cgallizzi/inkterface/design/feather-board.png

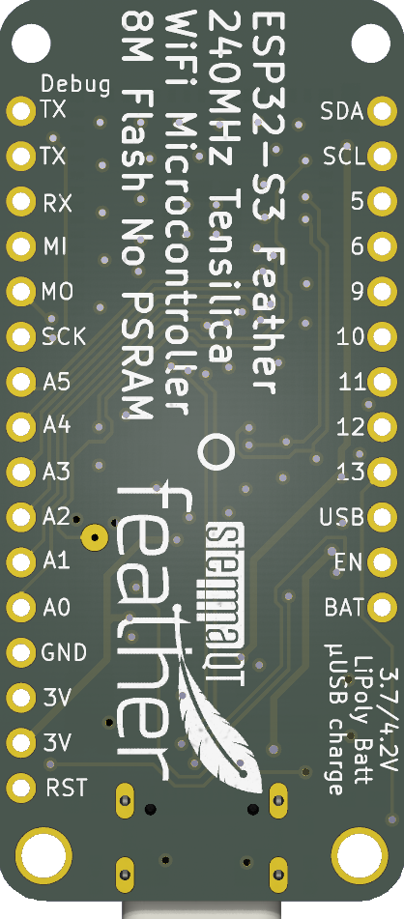
design/feather-board.png
