cgallizzi/inkterface/design/store-assets/Header_Capsule.png

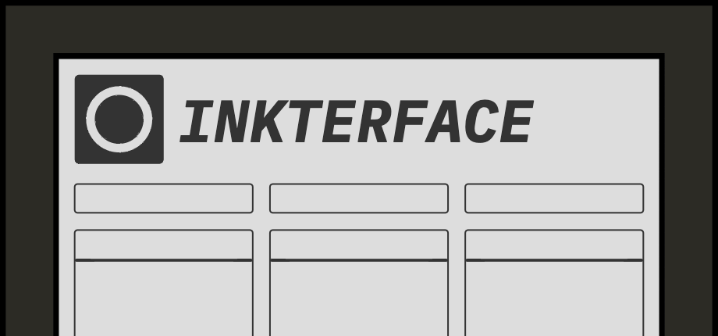
design/store-assets/Header_Capsule.png
