cgallizzi/inkterface/design/store-assets/Library_Capsule.png

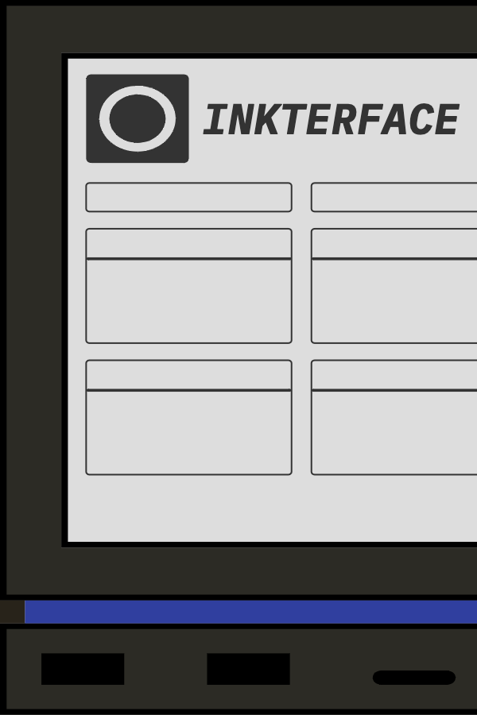
design/store-assets/Library_Capsule.png
