cgallizzi/inkterface/design/store-assets/Machine_Status.png

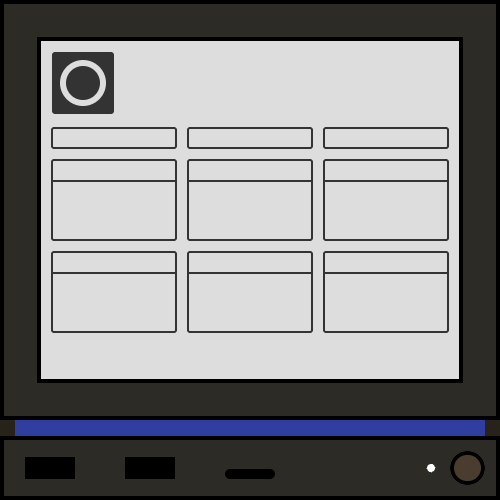
design/store-assets/Machine_Status.png
