cgallizzi/inkterface/design/store-assets/Small_Capsule.png

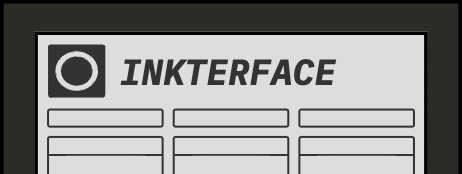
design/store-assets/Small_Capsule.png
