cgallizzi/inkterface/design/store-assets/Vertical_Capsule.png

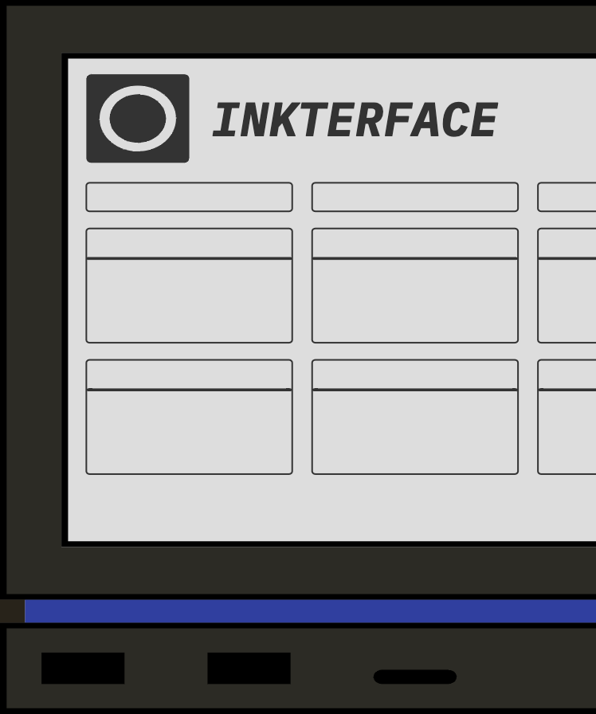
design/store-assets/Vertical_Capsule.png
