cgallizzi/inkterface/resources/gaben.png

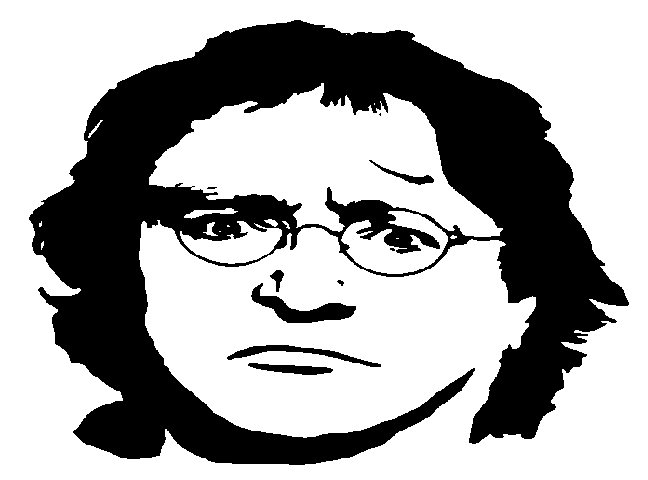
resources/gaben.png
