cgallizzi/inkterface/include/panel-state.hpp

#ifndef PANEL_STATE_HPP
#define PANEL_STATE_HPP

#include <algorithm>
#include <chrono>
#include <functional>
#include <limits>

#include <QObject>
#include <QPointF>
#include <QPointer>
#include <QSettings>
#include <QTimer>

#include "artwork.hpp"
#include "steam.hpp"
#include "sysstats.hpp"

#define PANEL_UPDATE_INTERVAL 2000
#define PANEL_POINT_DEPTH 20
#define PANEL_READOUT_COUNT 3
#define PANEL_SPARK_COUNT 6
#define PANEL_FIELD_COUNT (PANEL_READOUT_COUNT + PANEL_SPARK_COUNT)

using namespace Qt::Literals::StringLiterals;
using DblGetter = std::function<double()>;
using StrGetter = std::function<QString()>;
using Formatter = std::function<QString(double)>;

inline int64_t NOW_MS()
{
    return std::chrono::duration_cast<std::chrono::milliseconds>(
               std::chrono::system_clock::now().time_since_epoch())
        .count();
}

class PanelCollector : public QObject
{
    Q_OBJECT

    Q_PROPERTY(QString displayName READ displayName CONSTANT)
    Q_PROPERTY(QString panelName READ panelName CONSTANT)
    Q_PROPERTY(QString description READ description CONSTANT)
    Q_PROPERTY(bool hasDbl READ hasDbl CONSTANT)
    Q_PROPERTY(bool hasStr READ hasStr CONSTANT)

  public:
    explicit PanelCollector(const QString &disp, const QString &panel, const QString &desc,
                            DblGetter dg = nullptr, StrGetter sg = nullptr, Formatter fmt = nullptr,
                            QObject *parent = nullptr)
        : QObject(parent)
        , m_displayName(disp)
        , m_panelName(panel)
        , m_description(desc)
        , m_dblGetter(dg)
        , m_strGetter(sg)
        , m_formatter(fmt)
    {
        if (hasDbl() && m_formatter == nullptr) {
            m_formatter = [](double value) -> QString { return QString::number(value, 'f', 0); };
        }
    }

    const QString &displayName() const { return m_displayName; }
    const QString &panelName() const { return m_panelName; }
    const QString &description() const { return m_description; }
    bool hasDbl() const { return m_dblGetter != nullptr; }
    Q_INVOKABLE double getDbl(bool *ok = nullptr)
    {
        bool status = false;
        double result = 0;
        if (m_dblGetter) {
            status = true;
            result = m_dblGetter();
        }
        if (ok != nullptr) {
            *ok = status;
        }
        return result;
    }
    bool hasStr() const { return m_strGetter != nullptr || m_formatter != nullptr; }
    Q_INVOKABLE QString getStr(bool *ok = nullptr)
    {
        bool status = false;
        QString result;
        if (m_strGetter) {
            status = true;
            result = m_strGetter();
        } else if (m_dblGetter && m_formatter) {
            status = true;
            result = m_formatter(m_dblGetter());
        }
        if (ok != nullptr) {
            *ok = status;
        }
        return result;
    }

  private:
    QString m_displayName;
    QString m_panelName;
    QString m_description;
    DblGetter m_dblGetter;
    StrGetter m_strGetter;
    Formatter m_formatter;
};

class PanelField : public QObject
{
    Q_OBJECT

    Q_PROPERTY(QString key READ key NOTIFY readoutChanged)
    Q_PROPERTY(QString val READ val NOTIFY readoutChanged)

    Q_PROPERTY(int depth READ depth NOTIFY pointsChanged)
    Q_PROPERTY(QList<QPointF> points READ points NOTIFY pointsChanged)
    Q_PROPERTY(double xMax READ xMax NOTIFY pointsChanged)
    Q_PROPERTY(double xMin READ xMin NOTIFY pointsChanged)
    Q_PROPERTY(double yMax READ yMax NOTIFY pointsChanged)
    Q_PROPERTY(double yMin READ yMin NOTIFY pointsChanged)

    Q_PROPERTY(PanelCollector *collector READ collector WRITE setCollector NOTIFY collectorChanged)

  public:
    explicit PanelField(const int &index, const double &depth = 0, QObject *parent = nullptr)
        : QObject(parent)
        , m_index(index)
        , m_depth(depth)
    {
    }

    const QString &key() const { return m_key; }
    const QString &val() const { return m_val; }
    const int &depth() const { return m_depth; }
    const QList<QPointF> &points() const { return m_points; }
    const double &xMax() const { return m_xMax; }
    const double &xMin() const { return m_xMin; }
    const double &yMax() const { return m_yMax; }
    const double &yMin() const { return m_yMin; }
    QPointer<PanelCollector> collector() const { return m_collector; }

    void setCollector(QPointer<PanelCollector> collector)
    {
        if (m_collector != collector) {
            m_collector = collector;
            QSettings settings;
            settings.setValue(u"field%1Collector"_s.arg(QString::number(m_index)),
                              m_collector ? m_collector->displayName() : u""_s);
            emit collectorChanged();
            clear();
            if (m_collector) {
                m_key = m_collector->panelName();
                m_val = m_collector->getStr();
            }
            emit readoutChanged();
            emit pointsChanged();
        }
    }

    bool collect(const double &x = 0)
    {
        if (!m_collector)
            return false;
        QString k = m_collector->panelName();
        QString v = m_collector->getStr();
        bool changed = k != m_key || v != m_val;
        m_key = k;
        m_val = v;
        if (changed) {
            emit readoutChanged();
        }
        if (m_depth && m_collector->hasDbl()) {
            changed = true; // when we collect a new point it's always a change
            append(x, m_collector->getDbl());
            emit pointsChanged();
        }
        return changed;
    }

  signals:
    void readoutChanged();
    void pointsChanged();
    void collectorChanged();

  private:
    int m_index = 0;
    QString m_key;
    QString m_val;
    int m_depth = 20;
    QList<QPointF> m_points;
    double m_xMax = 0;
    double m_xMin = 0;
    double m_yMax = 0;
    double m_yMin = 0;
    QPointer<PanelCollector> m_collector;

    void append(const double &x, const double &y)
    {
        m_points.emplace_back(x, y);
        while (m_points.size() > m_depth) {
            m_points.pop_front();
        }
        // slow, recalc max/min, but we keep so few points it's not critical
        m_xMax = std::numeric_limits<double>::lowest();
        m_xMin = std::numeric_limits<double>::max();
        m_yMax = std::numeric_limits<double>::lowest();
        m_yMin = std::numeric_limits<double>::max();
        for (const auto &point : std::as_const(m_points)) {
            m_xMax = std::max(m_xMax, point.x());
            m_xMin = std::min(m_xMin, point.x());
            m_yMax = std::max(m_yMax, point.y());
            m_yMin = std::min(m_yMin, point.y());
        }
    }

    void clear()
    {
        m_key = u""_s;
        m_val = u""_s;
        m_points.clear();
        m_xMax = 0;
        m_xMin = 0;
        m_yMax = 0;
        m_yMin = 0;
    }
};

class PanelState : public QObject
{
    Q_OBJECT

    Q_PROPERTY(bool dirty READ dirty NOTIFY dataChanged)
    Q_PROPERTY(QString topLine READ topLine NOTIFY dataChanged)
    Q_PROPERTY(QString midLine READ midLine NOTIFY dataChanged)
    Q_PROPERTY(QString botLine READ botLine NOTIFY dataChanged)
    Q_PROPERTY(QList<PanelField *> fields READ fields NOTIFY fieldsChanged)
    Q_PROPERTY(QList<PanelCollector *> collectors READ collectors NOTIFY collectorsChanged)
    Q_PROPERTY(bool artworkEnabled READ artworkEnabled WRITE setArtworkEnabled NOTIFY
                   artworkEnabledChanged)

  public:
    explicit PanelState(QObject *parent = nullptr)
        : QObject(parent)
        , m_steam(new steam::Steam(this))
        , m_stats(new SysStats(this))
        , m_artwork(new Artwork(m_steam, this))
        , m_updateTimer(new QTimer(this))
    {
        // str only collectors
        registerCollector(u"OS Version"_s, u"OS"_s, u"Host operating system version."_s,
                          std::bind(&SysStats::getOSVersion, m_stats));
        registerCollector(u"BIOS Version"_s, u"BIOS"_s, u"Host BIOS version."_s,
                          std::bind(&SysStats::getBIOSVersion, m_stats));
        registerCollector(u"Steam Version"_s, u"STEAM"_s, u"Host Steam version."_s,
                          std::bind(&steam::Steam::steamVersion, m_steam));
        // double collectors that can be spark graphed
        registerCollector(u"App Count"_s, u"APPS"_s, u"Number of apps installed on the host."_s,
                          std::bind(&steam::Steam::installedAppCount, m_steam));
        registerCollector(u"Fan RPM"_s, u"FAN"_s, u"Host machine fan RPM."_s,
                          std::bind(&SysStats::getFanRPM, m_stats),
                          [](double v) { return u"%1 RPM"_s.arg(QString::number(v, 'f', 0)); });
        registerCollector(u"GPU Clock"_s, u"GPU SCLK"_s, u"GPU core clock speed in GHz."_s,
                          std::bind(&SysStats::getGPUSCLK, m_stats),
                          [](double v) { return u"%1 GHz"_s.arg(QString::number(v, 'f', 1)); });
        registerCollector(u"GPU Memory Clock"_s, u"GPU MCLK"_s, u"GPU memory clock speed in MHz."_s,
                          std::bind(&SysStats::getGPUSCLK, m_stats),
                          [](double v) { return u"%1 MHz"_s.arg(QString::number(v, 'f', 1)); });
        registerCollector(u"GPU Voltage"_s, u"GPU"_s, u"GPU core rail voltage."_s,
                          std::bind(&SysStats::getGPUV, m_stats),
                          [](double v) { return u"%1 V"_s.arg(QString::number(v, 'f', 3)); });
        registerCollector(u"GPU Power"_s, u"GPU"_s, u"GPU power consumption in Watts."_s,
                          std::bind(&SysStats::getGPUW, m_stats),
                          [](double v) { return u"%1 W"_s.arg(QString::number(v, 'f', 1)); });
        registerCollector(u"GPU Temperature"_s, u"GPU"_s, u"GPU junction temperature in C."_s,
                          std::bind(&SysStats::getGPUTemp, m_stats),
                          [](double v) { return u"%1 C"_s.arg(QString::number(v, 'f', 1)); });
        registerCollector(u"GPU Memory Temperature"_s, u"GPU MEM"_s,
                          u"GPU memory temperature in C."_s,
                          std::bind(&SysStats::getGPUMemTemp, m_stats),
                          [](double v) { return u"%1 C"_s.arg(QString::number(v, 'f', 1)); });
        registerCollector(u"GPU Memory"_s, u"GPU MEM"_s, u"GPU memory usage percent."_s,
                          std::bind(&SysStats::getGPUMemPerc, m_stats),
                          [](double v) { return u"%1%"_s.arg(QString::number(v, 'f', 0)); });
        registerCollector(u"GPU"_s, u"GPU"_s, u"GPU usage percent."_s,
                          std::bind(&SysStats::getGPUPerc, m_stats),
                          [](double v) { return u"%1%"_s.arg(QString::number(v, 'f', 0)); });
        registerCollector(u"SSD Temperature"_s, u"SSD"_s, u"SSD temperature in C."_s,
                          std::bind(&SysStats::getSSDTemp, m_stats),
                          [](double v) { return u"%1 C"_s.arg(QString::number(v, 'f', 1)); });
        registerCollector(u"CPU Temperature"_s, u"CPU"_s, u"CPU temperature in C."_s,
                          std::bind(&SysStats::getCPUTemp, m_stats),
                          [](double v) { return u"%1 C"_s.arg(QString::number(v, 'f', 1)); });
        registerCollector(u"CPU"_s, u"CPU"_s, u"CPU usage percent."_s,
                          std::bind(&SysStats::getCPUPerc, m_stats),
                          [](double v) { return u"%1%"_s.arg(QString::number(v, 'f', 0)); });
        registerCollector(u"CPU Frequency"_s, u"CPU"_s, u"Average CPU core frequency in GHz."_s,
                          std::bind(&SysStats::getCPUCLK, m_stats),
                          [](double v) { return u"%1 GHz"_s.arg(QString::number(v, 'f', 1)); });
        registerCollector(u"Memory"_s, u"MEM"_s, u"System memory usage percent."_s,
                          std::bind(&SysStats::getRAMPerc, m_stats),
                          [](double v) { return u"%1%"_s.arg(QString::number(v, 'f', 0)); });
        registerCollector(u"Uptime"_s, u"UPTIME"_s, u"System uptime in seconds."_s,
                          std::bind(&SysStats::getUptime, m_stats),
                          [](double v) { return u"%1 S"_s.arg(QString::number(v, 'f', 0)); });
        registerCollector(u"Game Time"_s, u"PLAYED"_s,
                          u"Total playtime of the currently running game."_s, [this]() -> QString {
                              const auto &app = m_steam->runningApp();
                              if (app.appid.isEmpty()) {
                                  return u"--"_s;
                              }
                              const double minutes = m_steam->appPlaytimeMinutes(app.appid);
                              if (minutes < 0) {
                                  return u"--"_s;
                              } else if (minutes < 60) {
                                  return u"%1 MIN"_s.arg(QString::number(minutes, 'f', 0));
                              }
                              return u"%1 HRS"_s.arg(QString::number(minutes / 60.0, 'f', 1));
                          });
        registerCollector(u"Achievements"_s, u"ACHIEVE"_s,
                          u"Achievements unlocked in the currently running game."_s,
                          [this]() -> QString {
                              const auto &app = m_steam->runningApp();
                              const auto counts = m_steam->achievements(app.appid);
                              if (app.appid.isEmpty() || counts.second <= 0) {
                                  return u"--"_s;
                              }
                              return u"%1/%2"_s.arg(QString::number(counts.first),
                                                    QString::number(counts.second));
                          });

        /* other ideas for things to track/display:
         *  active download progress as discrete bar
         *  quote of the day
         *  gabe/gnomekyle faces
         *  steampal-chan face
         *  clock (analog and digital, updates every minute)
         *  portal sentry eye
         *  companion cube
         *  literal easter egg
         *  weather display (need to pickup location or allow setting location)
         *  top style readout (likely top n-processes aggregated over like 30+ seconds)
         *  show connected controllers, just steam controller initially, other HID devices
         *      could be identified later or added by community
         */

        connect(m_steam, &steam::Steam::appStarted, this, &PanelState::onAppStarted);
        connect(m_steam, &steam::Steam::appStopped, this, &PanelState::onAppStopped);
        connect(m_steam, &steam::Steam::achievementsUpdated, this,
                &PanelState::onAchievementsUpdated);
        connect(m_artwork, &Artwork::frameReady, this, &PanelState::artworkFrame);
        m_steam->watchConsoleLog(true);

        // TODO: allow configuring different numbers/layouts of fields
        PanelField *field = nullptr;
        for (int i = 0; i < PANEL_FIELD_COUNT; ++i) {
            if (i < PANEL_READOUT_COUNT) {
                field = new PanelField(i, 0, this);
            } else {
                field = new PanelField(i, PANEL_POINT_DEPTH, this);
            }
            m_fields.append(field);
        }
        connect(m_updateTimer, &QTimer::timeout, this, &PanelState::updateState);
        m_updateTimer->setInterval(PANEL_UPDATE_INTERVAL);
        m_updateTimer->setSingleShot(false);
        updateState();
        m_updateTimer->start();
    }

    bool dirty() const { return m_dirty; }
    const QString &topLine() const { return m_topLine; }
    const QString &midLine() const { return m_midLine; }
    const QString &botLine() const { return m_botLine; }
    const QList<PanelField *> fields() const { return m_fields; }
    const QList<PanelCollector *> collectors() const { return m_collectors; }

    void registerCollector(const QString &displayName, const QString &panelName,
                           const QString &description, DblGetter getter, Formatter fmt = nullptr)
    {
        auto collector =
            new PanelCollector(displayName, panelName, description, getter, nullptr, fmt, this);
        m_collectors.append(collector);
        m_collectorMap[displayName] = collector;
        emit collectorsChanged();
    }
    void registerCollector(const QString &displayName, const QString &panelName,
                           const QString &description, StrGetter getter)
    {
        auto collector =
            new PanelCollector(displayName, panelName, description, nullptr, getter, nullptr, this);
        m_collectors.append(collector);
        m_collectorMap[displayName] = collector;
        emit collectorsChanged();
    }

    bool artworkEnabled() const
    {
        QSettings settings;
        return settings.value(u"artworkEnabled"_s, true).toBool();
    }
    void setArtworkEnabled(bool enabled)
    {
        if (enabled == artworkEnabled()) {
            return;
        }
        QSettings settings;
        settings.setValue(u"artworkEnabled"_s, enabled);
        emit artworkEnabledChanged();
        const auto &app = m_steam->runningApp();
        if (!enabled) {
            emit artworkClear();
        } else if (!app.appid.isEmpty()) {
            m_artwork->composeForApp(app, m_steam->appPlaytimeMinutes(app.appid),
                                     m_steam->achievements(app.appid));
        }
    }

  signals:
    void dataChanged();
    void fieldsChanged();
    void collectorsChanged();
    void artworkEnabledChanged();
    // a composed 1bpp frame ready to be pushed to the panel
    void artworkFrame(QByteArray bits, quint16 width, quint16 height);
    // the panel should fall back to the telemetry layout
    void artworkClear();

  public slots:
    void start() { m_updateTimer->start(); }
    void stop() { m_updateTimer->stop(); }
    void updateState()
    {
        bool changed = linkFieldCollectors();

        // top line is hostname from machine
        // TODO: allow configuring this
        changed |= m_topLine != m_stats->getHostName();
        m_topLine = m_stats->getHostName();

        // mid line is the most recent steam user
        // TODO: allow configuring this
        changed |= m_midLine != m_steam->currentUser();
        m_midLine = m_steam->currentUser();

        // bottom line is currently running app info
        // TODO: allow configuring this
        // TODO: add full utf-8 support to the e-ink font
        QString botLine;
        auto app = m_steam->runningApp();
        for (QChar c : std::as_const(app.name)) {
            if (c.unicode() <= 127) {
                botLine.append(c);
            }
        }
        changed |= m_botLine != botLine;
        m_botLine = botLine;

        // collect new data into fields (for all fields that have collectors)
        double x = NOW_MS();
        for (auto field : std::as_const(m_fields)) {
            changed |= field->collect(x);
        }

        if (changed) {
            m_dirty = true;
            emit dataChanged();
        }
    }

  private slots:
    void onAppStarted(steam::App details)
    {
        m_steam->fetchAchievements(details.appid);
        if (artworkEnabled()) {
            m_artwork->composeForApp(details, m_steam->appPlaytimeMinutes(details.appid),
                                     m_steam->achievements(details.appid));
        }
        updateState();
    }
    void onAppStopped([[maybe_unused]] steam::App details)
    {
        emit artworkClear();
        updateState();
    }
    void onAchievementsUpdated(QString appid)
    {
        const auto &app = m_steam->runningApp();
        if (artworkEnabled() && !app.appid.isEmpty() && app.appid == appid) {
            m_artwork->composeForApp(app, m_steam->appPlaytimeMinutes(app.appid),
                                     m_steam->achievements(app.appid));
        }
        updateState();
    }

  private:
    steam::Steam *m_steam = nullptr;
    SysStats *m_stats = nullptr;
    Artwork *m_artwork = nullptr;
    QTimer *m_updateTimer = nullptr;

    bool m_dirty = false;
    QString m_topLine;
    QString m_midLine;
    QString m_botLine;
    QList<PanelField *> m_fields;
    QList<PanelCollector *> m_collectors;
    QMap<QString, QPointer<PanelCollector>> m_collectorMap;

    // TODO: this can probably be public or get triggered if when a new collector
    //       is registered
    bool linkFieldCollectors()
    {
        bool changed = false;
        QSettings settings;
        QString collectorName;
        PanelField *field = nullptr;
        for (int i = 0; i < m_fields.size(); ++i) {
            field = m_fields[i];
            // TODO: this is lame, but i want the value in the settings file to
            //       be human readable, probably we should just enforce unique
            //       display names when registering collectors and leave it at that.
            collectorName = settings.value(u"field%1Collector"_s.arg(i)).toString();
            // NOTE: these are just arbitrary defaults
            if (collectorName.isEmpty()) {
                switch (i) {
                case 0:
                    collectorName = u"OS Version"_s;
                    break;
                case 1:
                    collectorName = u"BIOS Version"_s;
                    break;
                case 2:
                    collectorName = u"Steam Version"_s;
                    break;
                case 3:
                    collectorName = u"CPU Temperature"_s;
                    break;
                case 4:
                    collectorName = u"GPU Temperature"_s;
                    break;
                case 5:
                    collectorName = u"Fan RPM"_s;
                    break;
                case 6:
                    collectorName = u"CPU"_s;
                    break;
                case 7:
                    collectorName = u"GPU"_s;
                    break;
                case 8:
                    collectorName = u"Memory"_s;
                    break;
                }
            }
            if (!field->collector() || field->collector()->displayName() != collectorName) {
                changed = true;
                field->setCollector(m_collectorMap[collectorName]);
            }
        }
        return changed;
    }
};

#endif /* PANEL_STATE_HPP */
